openKolibri/halo-90/docs/artwork/cardBack.png

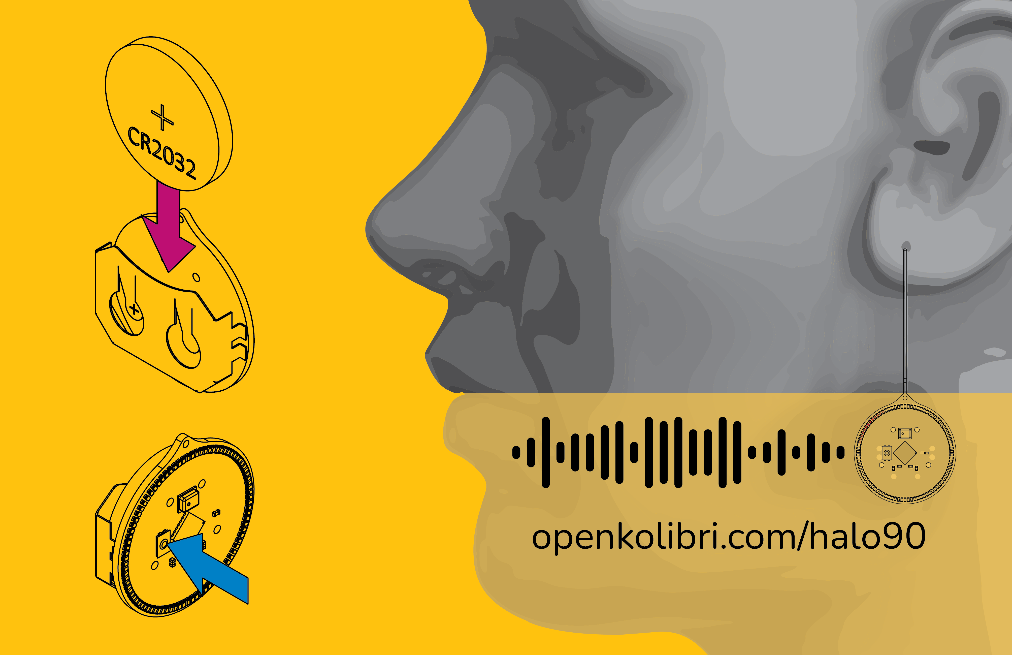
docs/artwork/cardBack.png
