openKolibri/halo-90/docs/artwork/cardFront.png

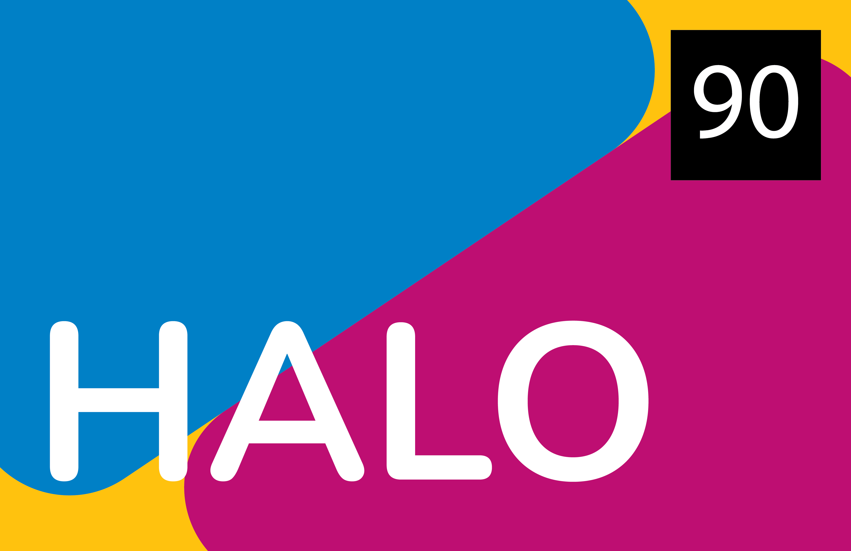
docs/artwork/cardFront.png
