openKolibri/halo-90/docs/case/batch.jpg

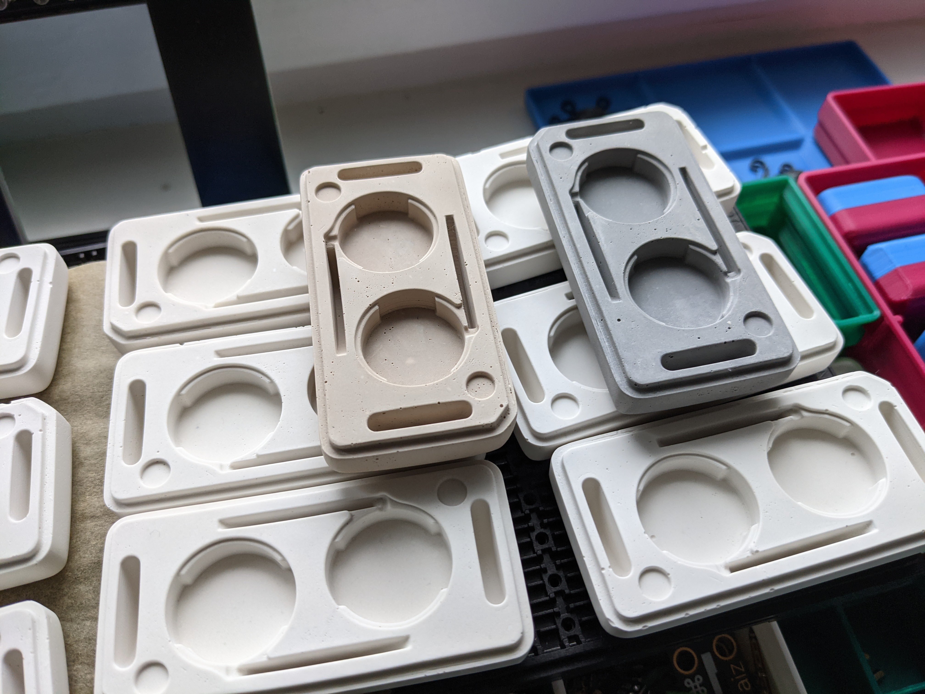
docs/case/batch.jpg
