openKolibri/halo-90/docs/case/caseRender.jpg

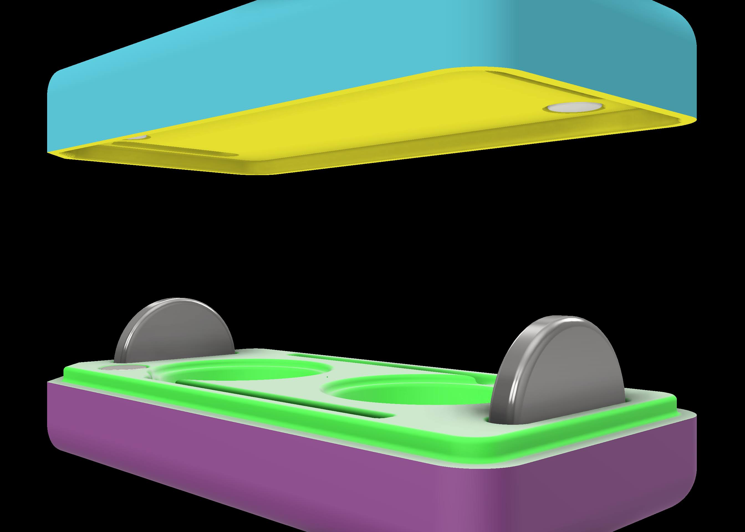
docs/case/caseRender.jpg
