openKolibri/halo-90/docs/case/cases.jpg

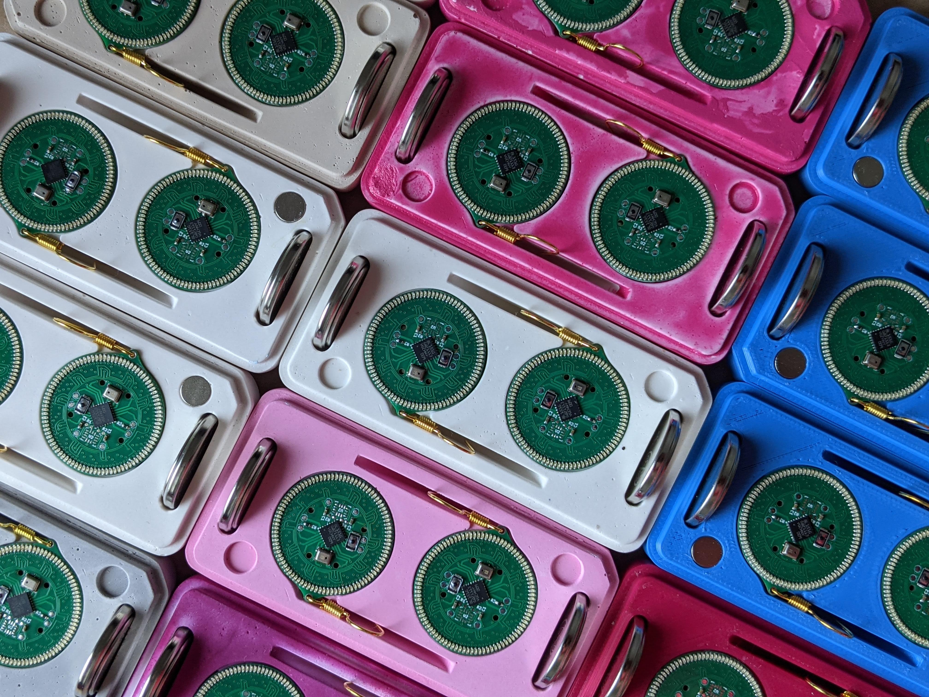
docs/case/cases.jpg
