openKolibri/halo-90/docs/case/casting.jpg

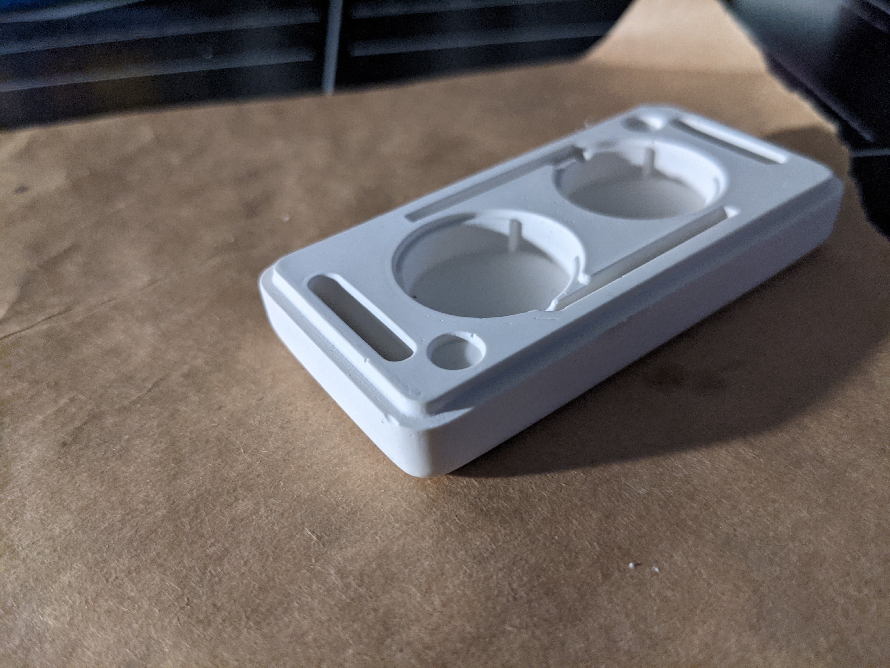
docs/case/casting.jpg
