openKolibri/halo-90/docs/case/master.jpg

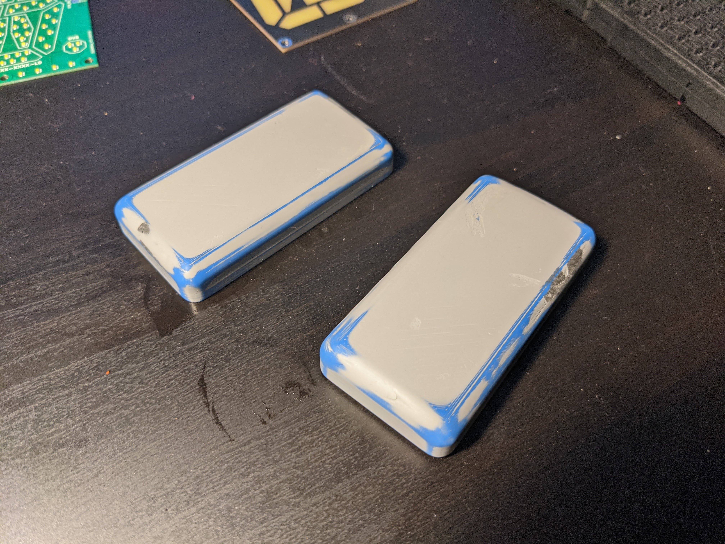
docs/case/master.jpg
