openKolibri/halo-90/docs/case/mould.jpg

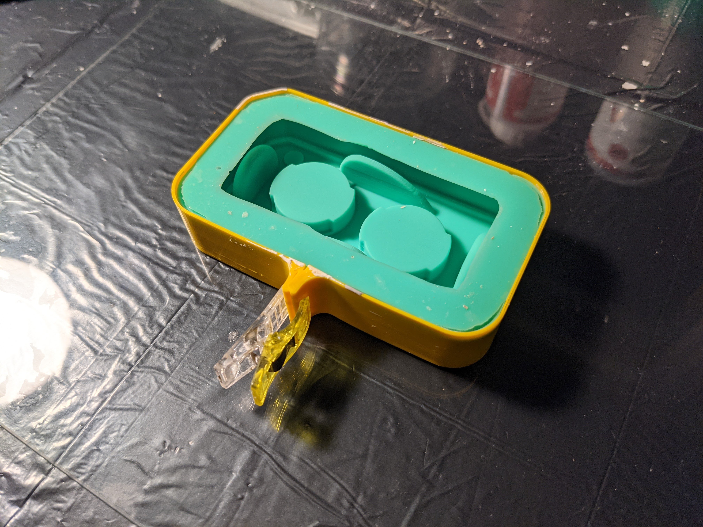
docs/case/mould.jpg
