openKolibri/halo-90/docs/connectors/mass.jpg

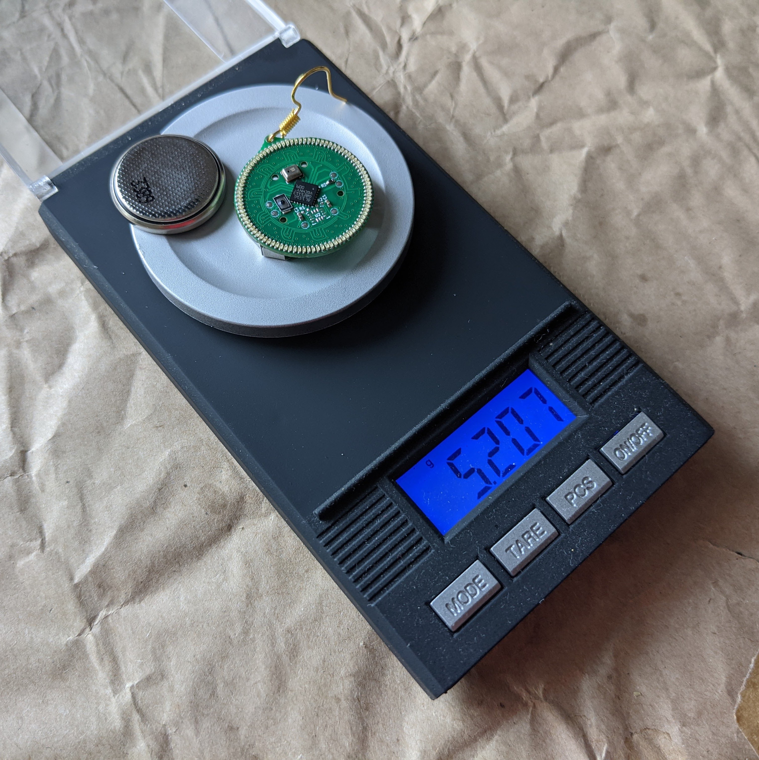
docs/connectors/mass.jpg
