openKolibri/halo-90/docs/connectors/pinDim.jpg

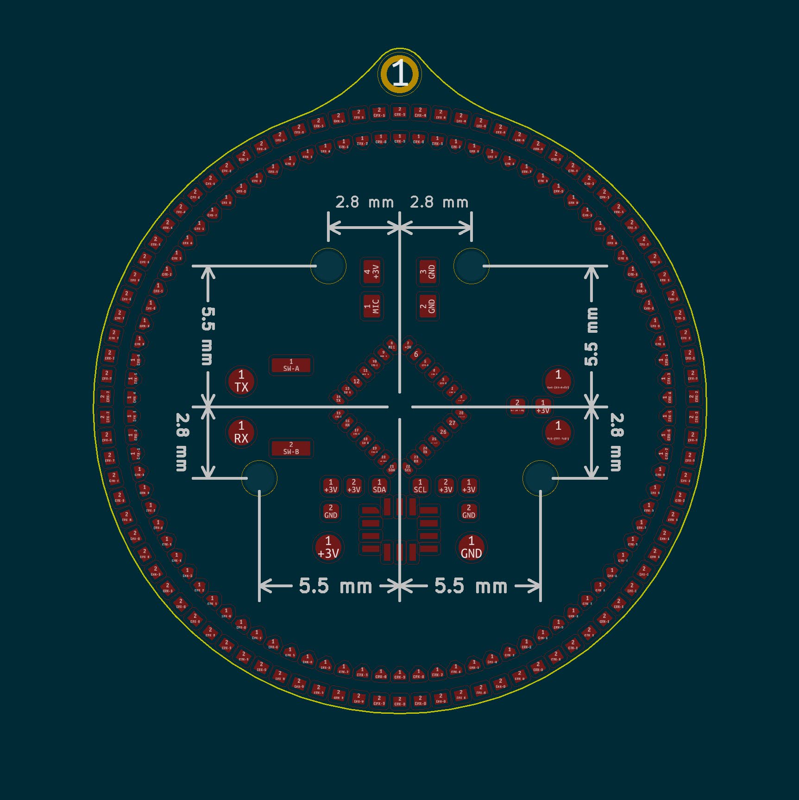
docs/connectors/pinDim.jpg
