openKolibri/halo-90/docs/firmware/boot.gif

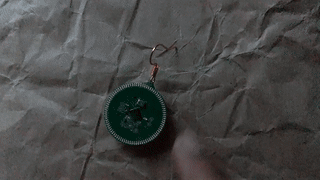
docs/firmware/boot.gif
