openKolibri/halo-90/docs/firmware/powerProfile/audio.gif

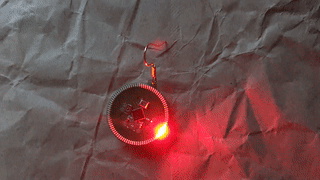
docs/firmware/powerProfile/audio.gif
