openKolibri/halo-90/docs/firmware/powerProfile/audioPowerProfile.png

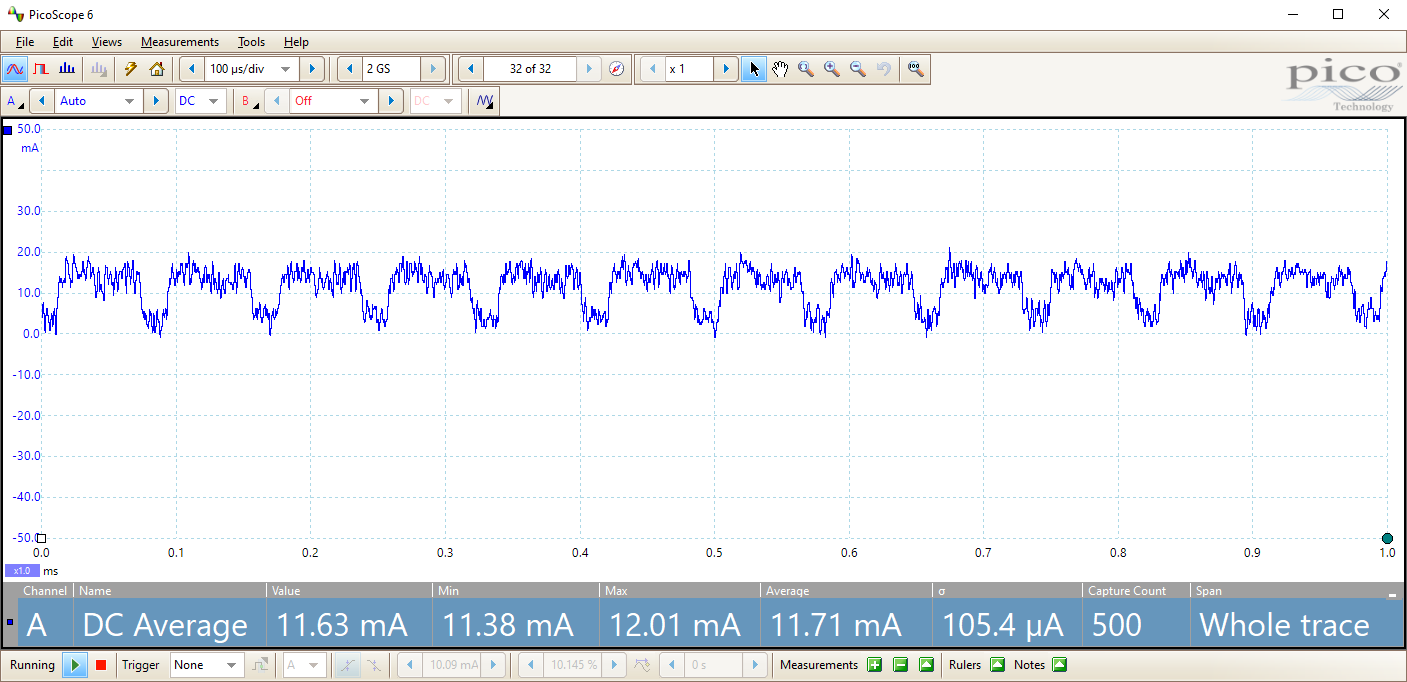
docs/firmware/powerProfile/audioPowerProfile.png
