openKolibri/halo-90/docs/firmware/powerProfile/halo.gif

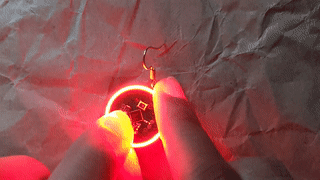
docs/firmware/powerProfile/halo.gif
