openKolibri/halo-90/docs/firmware/powerProfile/haloPowerProfile.png

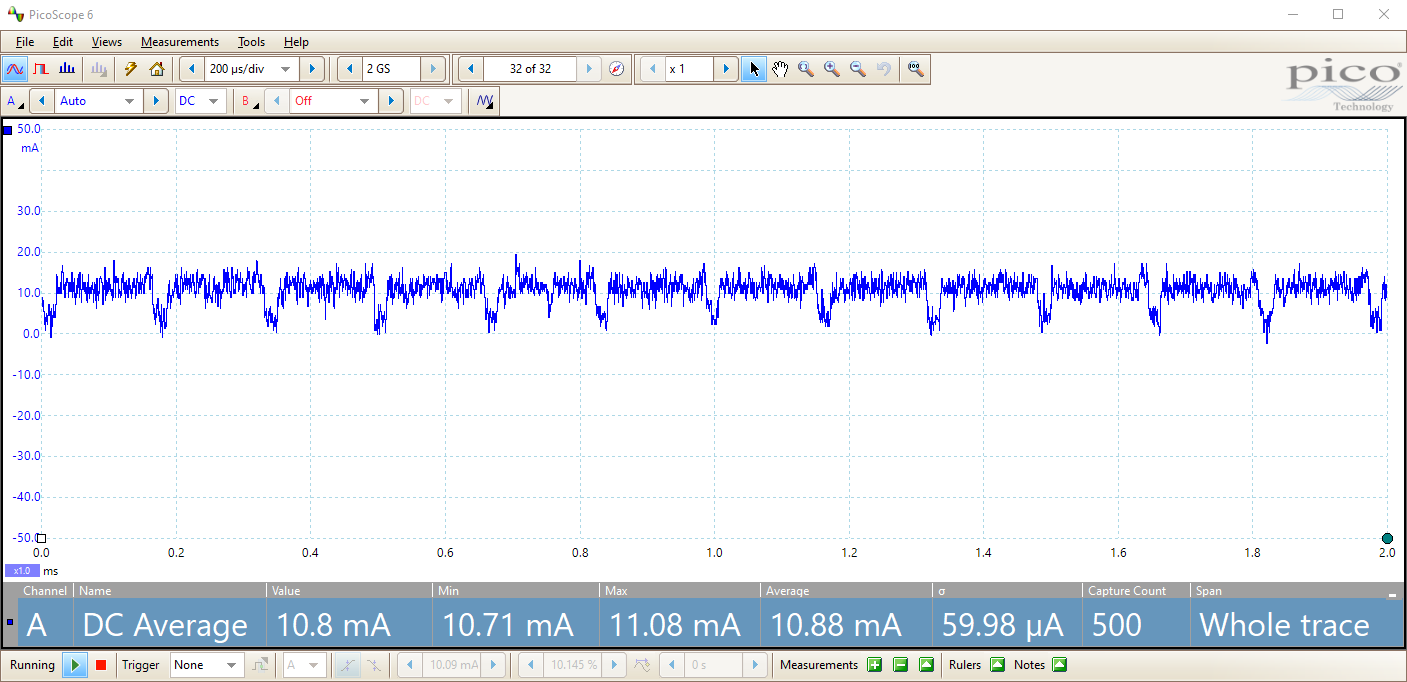
docs/firmware/powerProfile/haloPowerProfile.png
