openKolibri/halo-90/docs/firmware/powerProfile/sparkle.gif

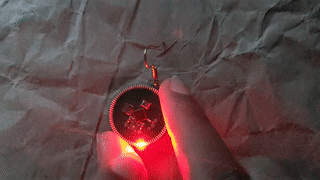
docs/firmware/powerProfile/sparkle.gif
