openKolibri/halo-90/docs/firmware/powerProfile/sparklePowerProfile.png

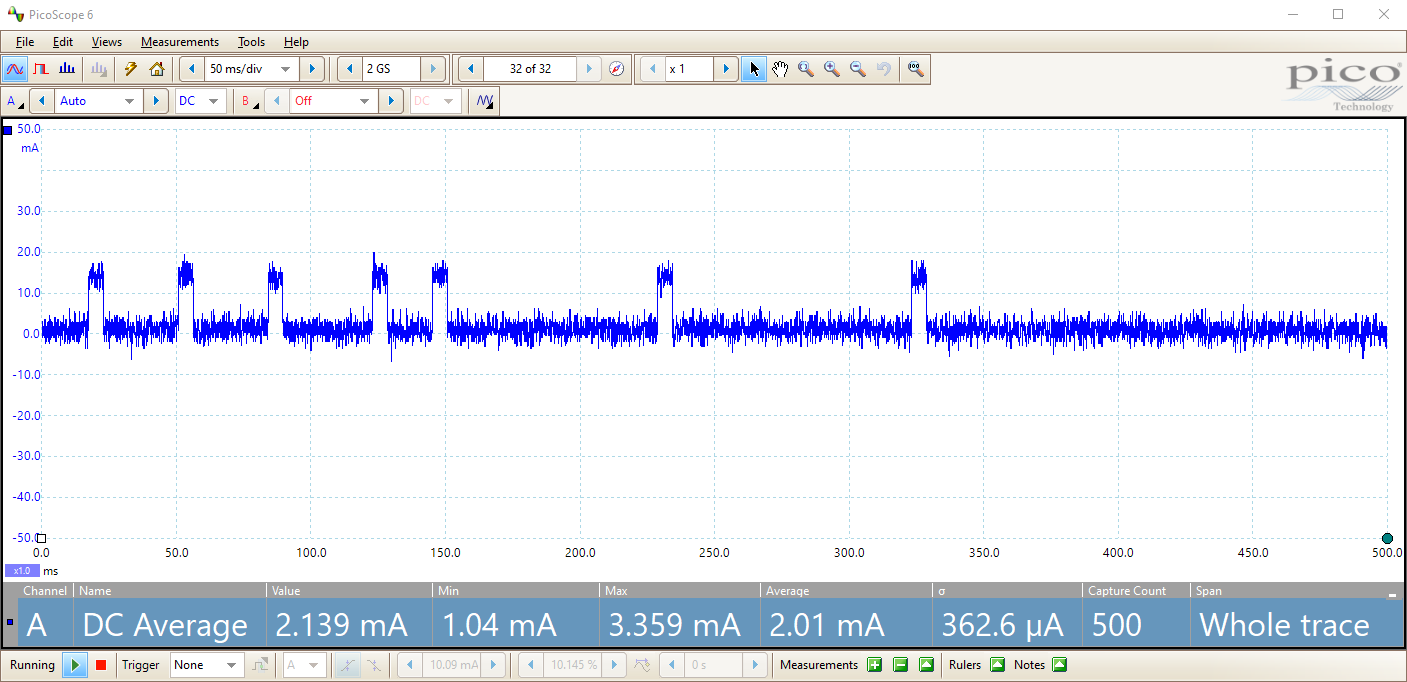
docs/firmware/powerProfile/sparklePowerProfile.png
