openKolibri/halo-90/docs/intro/haloSetDisplay.jpg

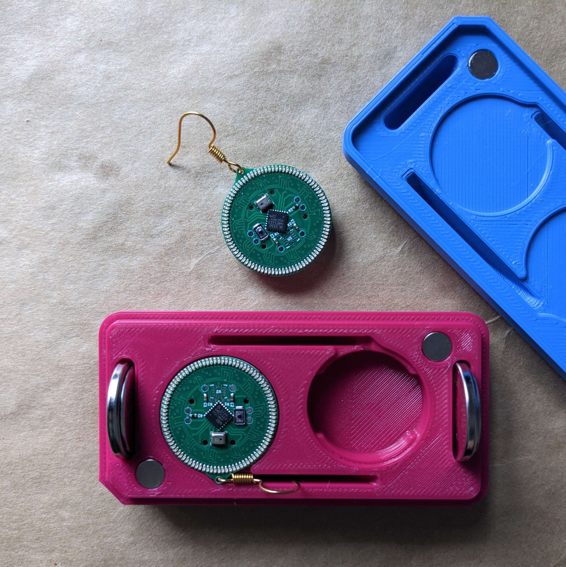
docs/intro/haloSetDisplay.jpg
