openKolibri/halo-90/docs/layers/L0.png

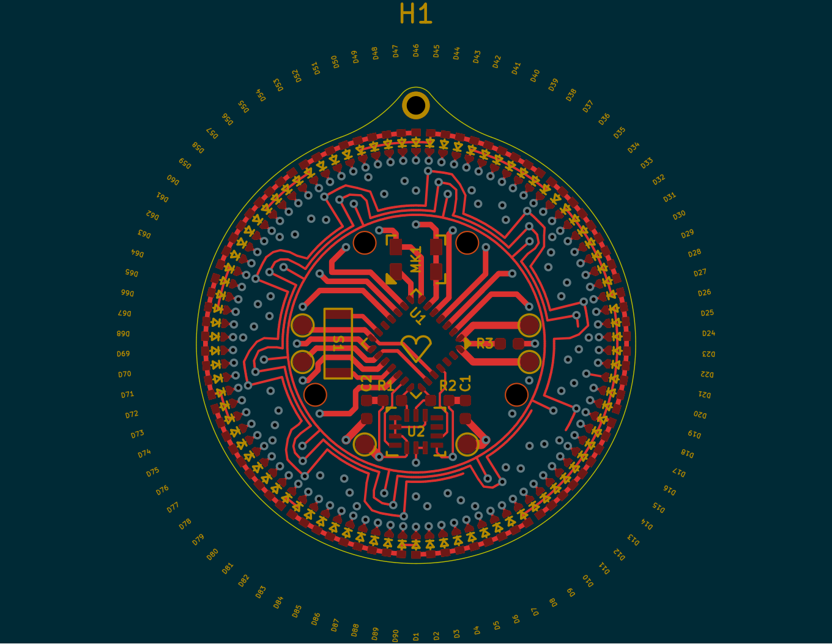
docs/layers/L0.png
