openKolibri/halo-90/docs/layers/L1.png

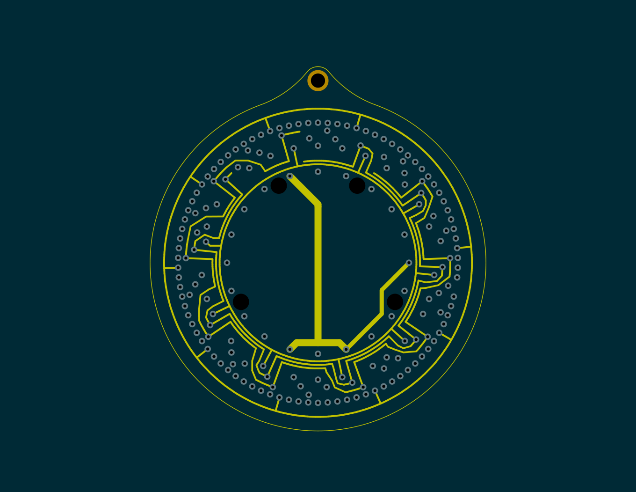
docs/layers/L1.png
