openKolibri/halo-90/docs/layers/L2.png

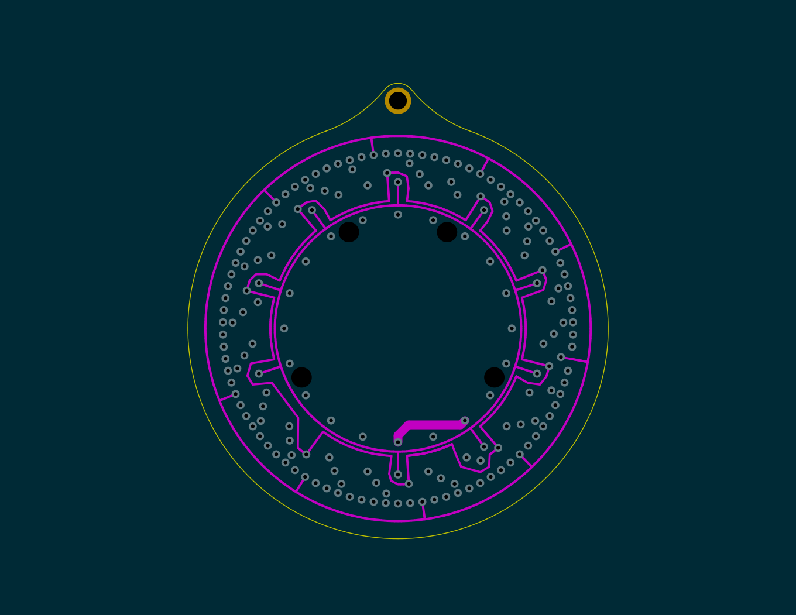
docs/layers/L2.png
