openKolibri/halo-90/docs/layers/L3.png

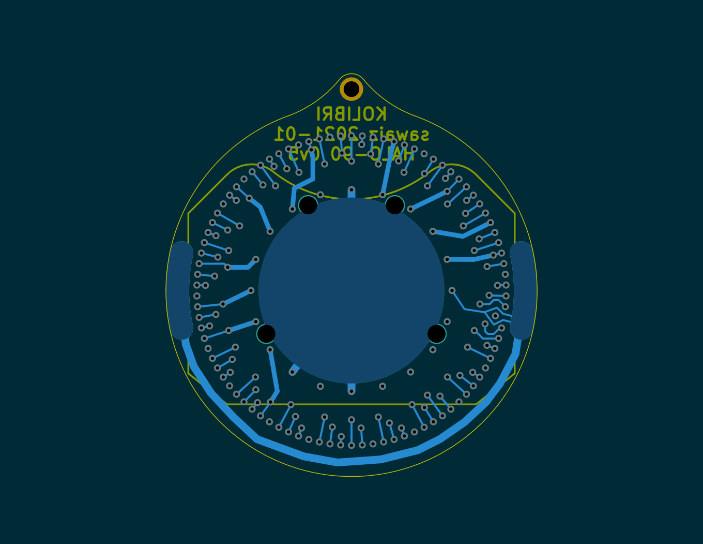
docs/layers/L3.png
