openKolibri/halo-90/docs/patterns/halo.gif

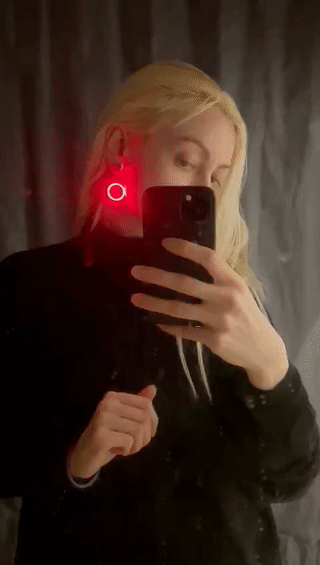
docs/patterns/halo.gif
