openKolibri/halo-90/docs/programmer.jpg

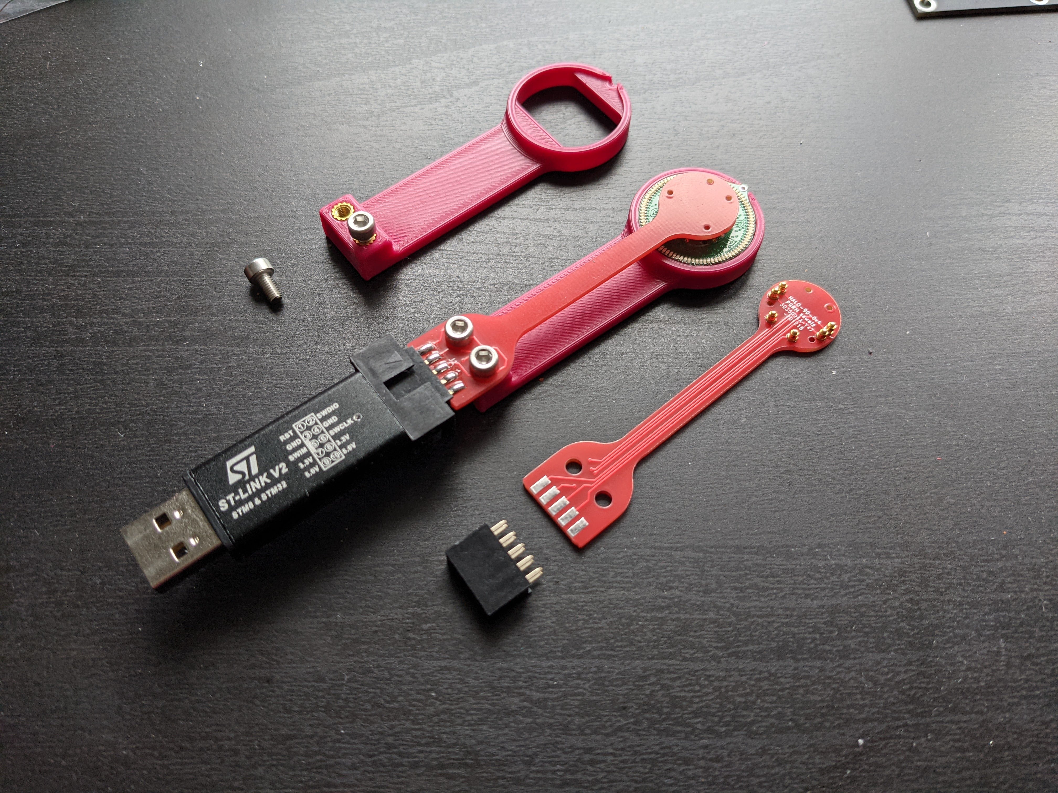
docs/programmer.jpg
