openKolibri/halo-90/docs/render.jpg

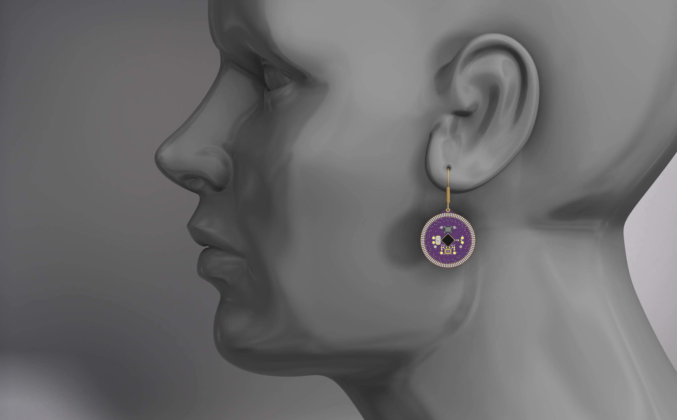
docs/render.jpg
