openKolibri/halo-90/docs/components/magnets.jpg

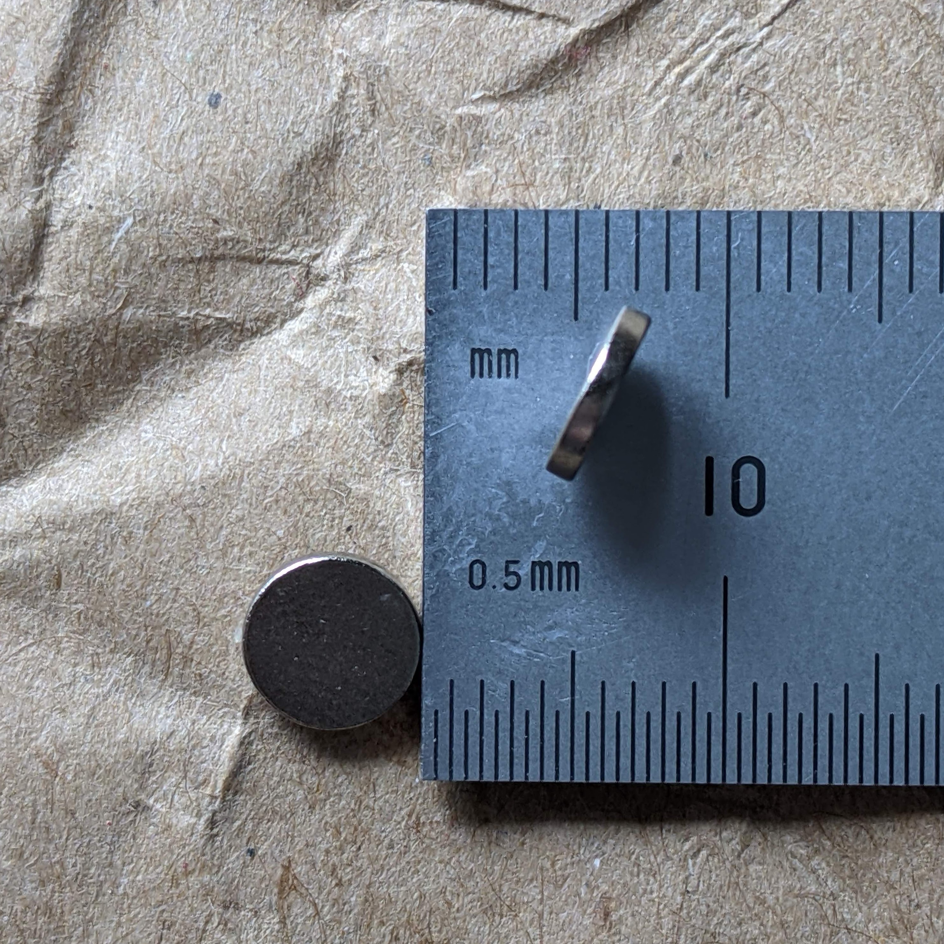
docs/components/magnets.jpg
