openKolibri/halo-90/pcb/components/BAT-HLD-001/BAT-HLD-001.jpg

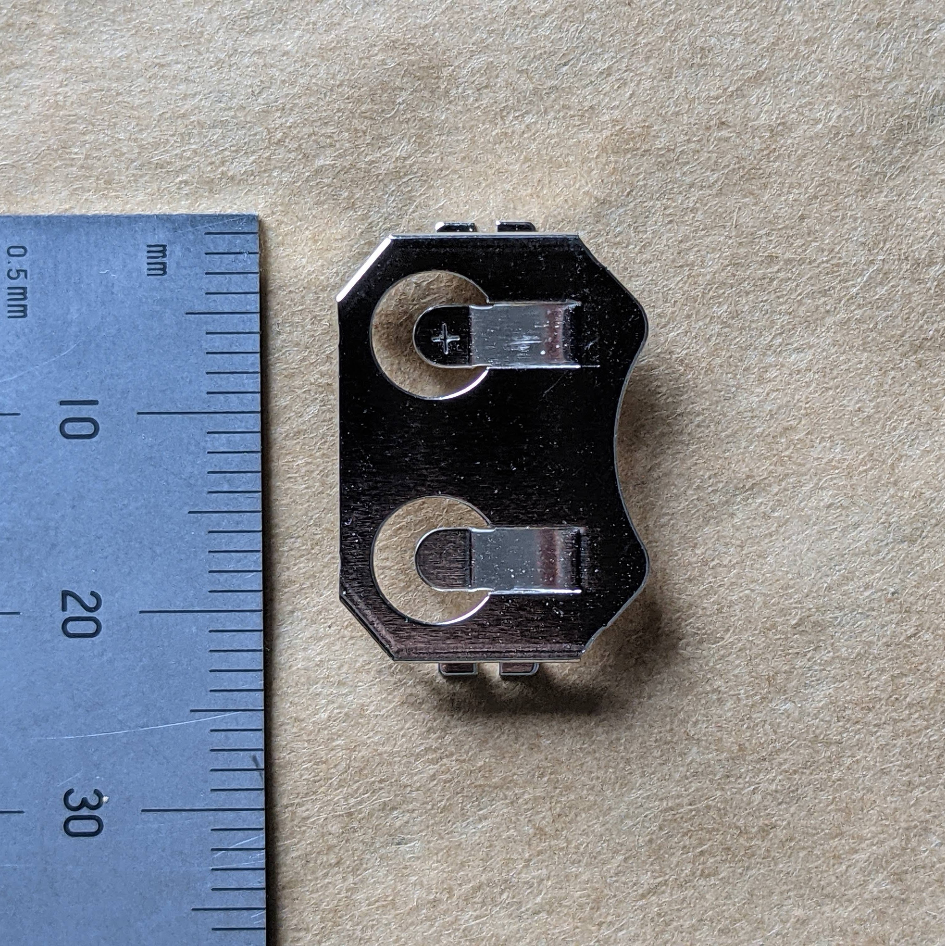
pcb/components/BAT-HLD-001/BAT-HLD-001.jpg
