openKolibri/halo-90/pcb/components/frenchEarwire/frenchEarwire.jpg

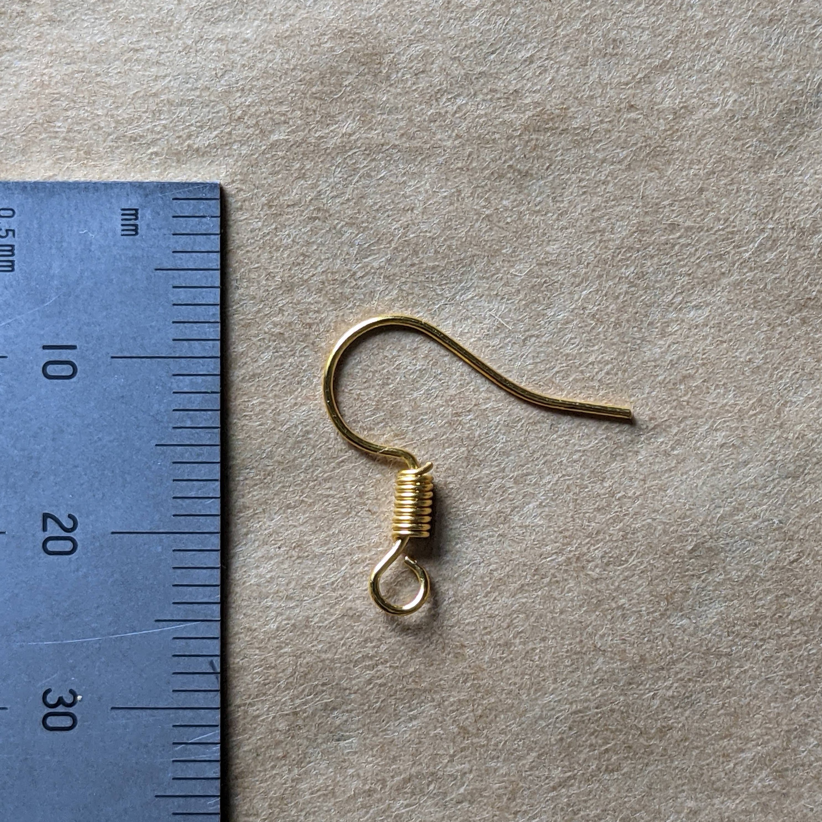
pcb/components/frenchEarwire/frenchEarwire.jpg
