openKolibri/halo-90/pcb/components/KXT3/KXT3.jpg

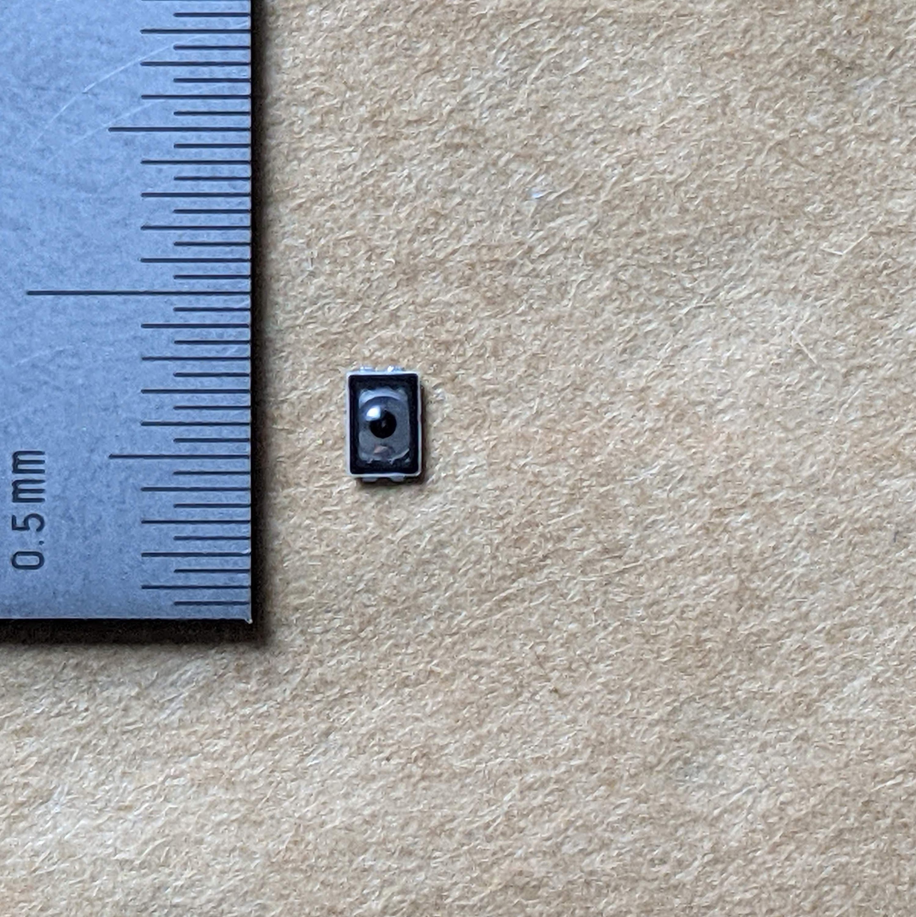
pcb/components/KXT3/KXT3.jpg
