openKolibri/halo-90/pcb/components/LSM6DSM/LSM6DSM.jpg

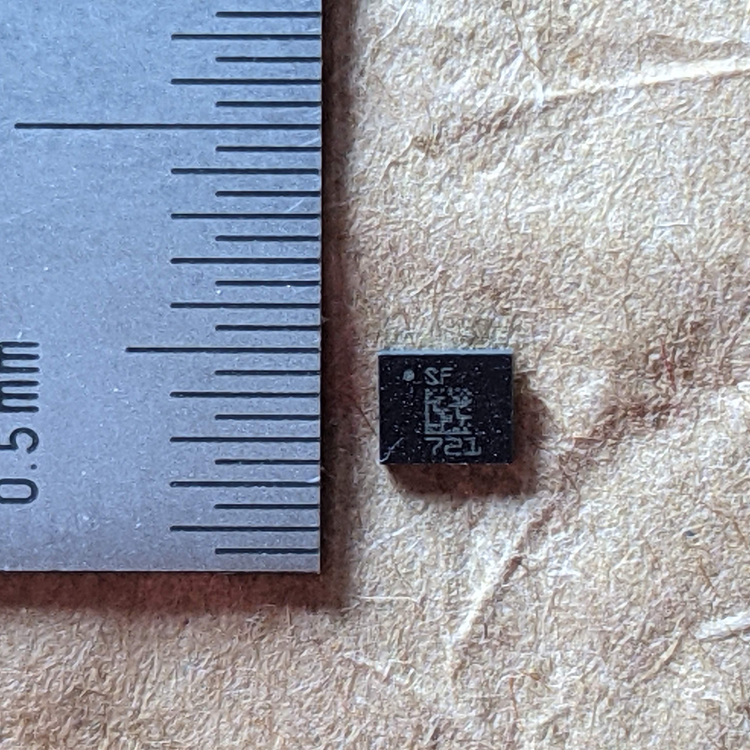
pcb/components/LSM6DSM/LSM6DSM.jpg
