openKolibri/halo-90/pcb/components/SPW2430HR5H-B/SPW2430HR5H-B.jpg

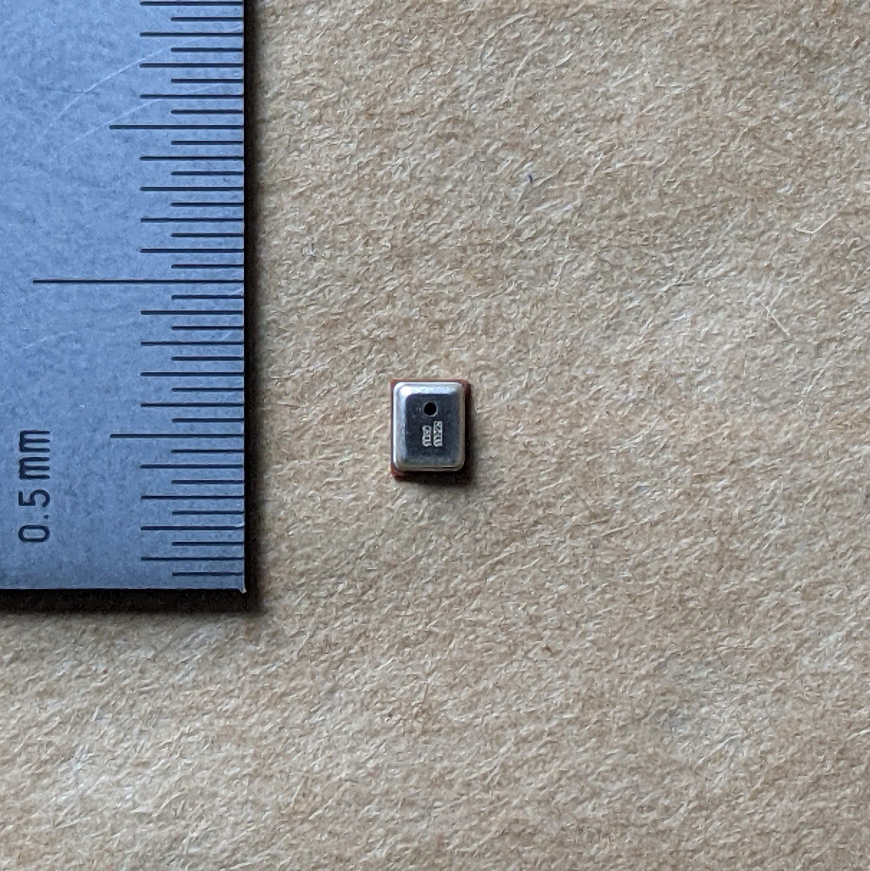
pcb/components/SPW2430HR5H-B/SPW2430HR5H-B.jpg
