openKolibri/halo-90/pcb/components/STM8L15xxx/STM8L15xxx.jpg

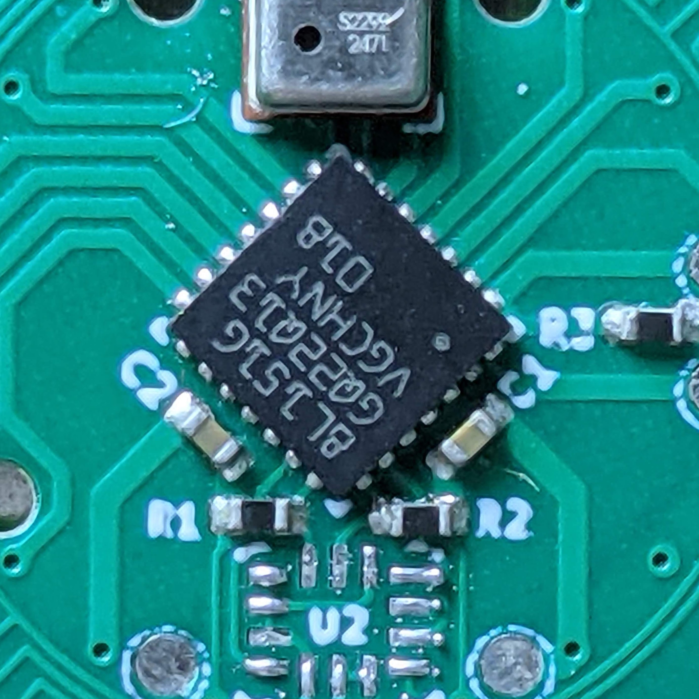
pcb/components/STM8L15xxx/STM8L15xxx.jpg
