openKolibri/halo-90/pcb/components/passives/L-0805.stp

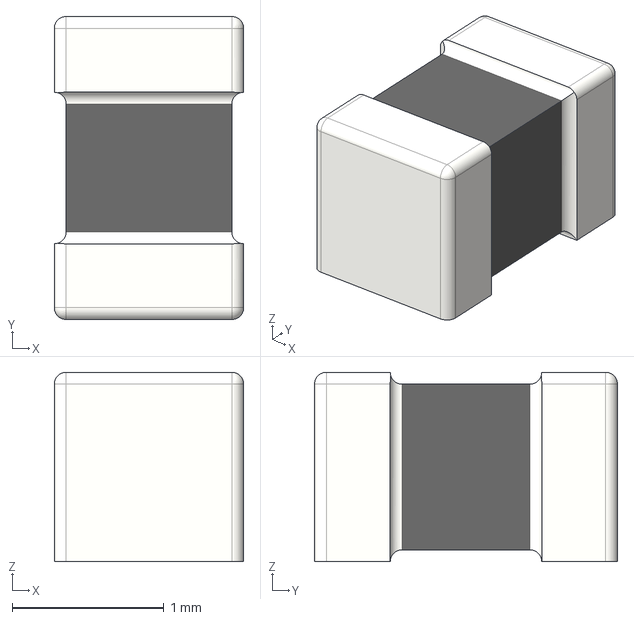
[picture p52: CAD file, 2021-01-04]
pcb/components/passives/L-0805.stp
1.25 x 2.00 x 1.25 mm
