openKolibri/halo-90/pcb/components/passives/C-0201.stp

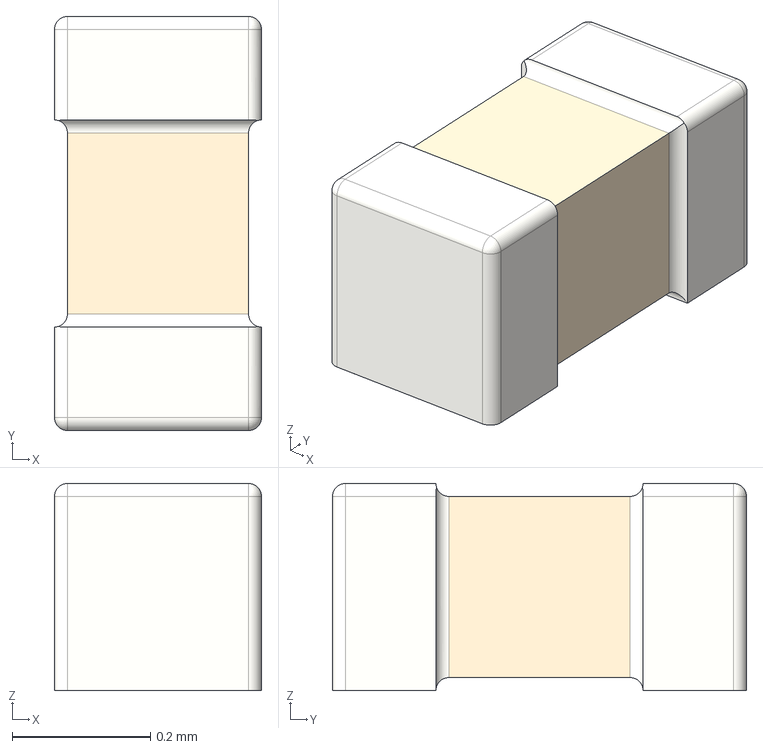
[picture p53: CAD file, 2021-01-04]
pcb/components/passives/C-0201.stp
0.3 x 0.6 x 0.3 mm
