openKolibri/halo-90/pcb/components/passives/R-0603.stp

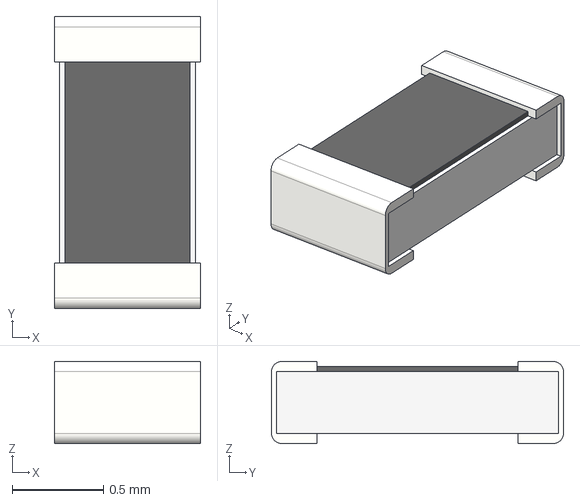
[picture p54: CAD file, 2021-01-04]
pcb/components/passives/R-0603.stp
0.8 x 1.60 x 0.45 mm
