openKolibri/halo-90/pcb/components/passives/L-0603.stp

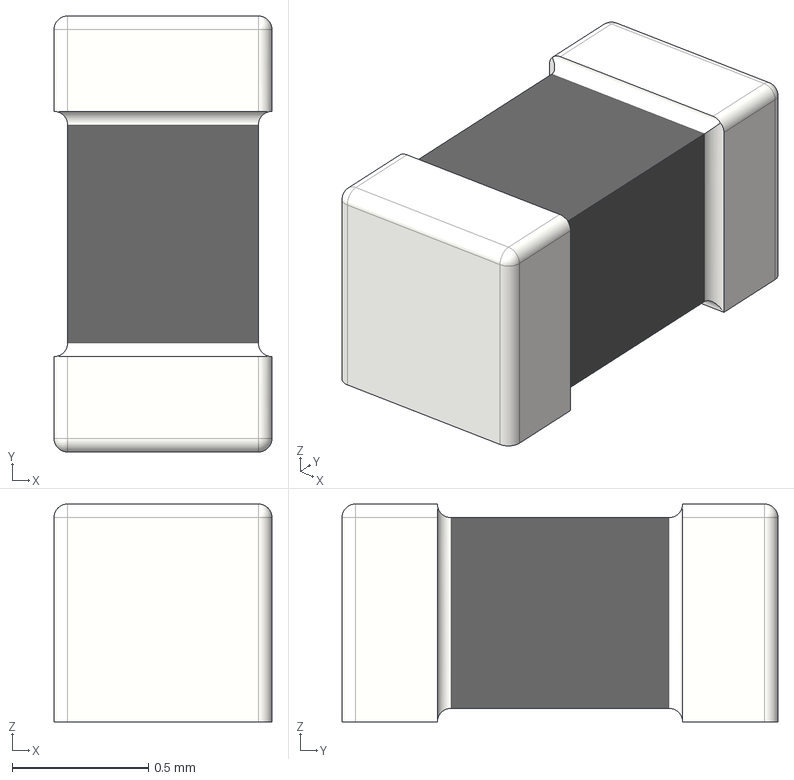
[picture p55: CAD file, 2021-01-04]
pcb/components/passives/L-0603.stp
0.8 x 1.60 x 0.8 mm
