openKolibri/halo-90/pcb/components/passives/C-2220.stp

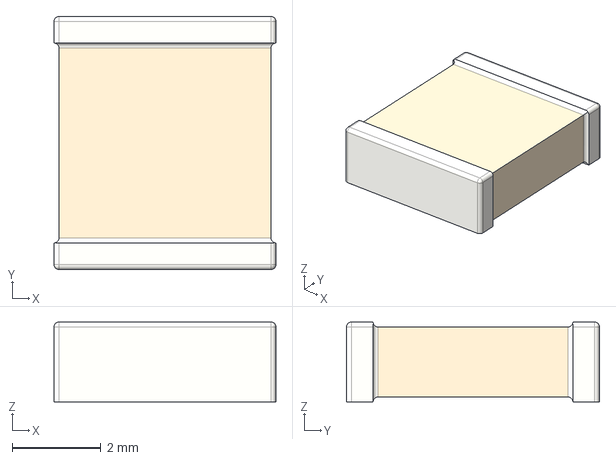
[picture p56: CAD file, 2021-01-04]
pcb/components/passives/C-2220.stp
5.00 x 5.70 x 1.80 mm
