openKolibri/halo-90/pcb/components/passives/C-0805.stp

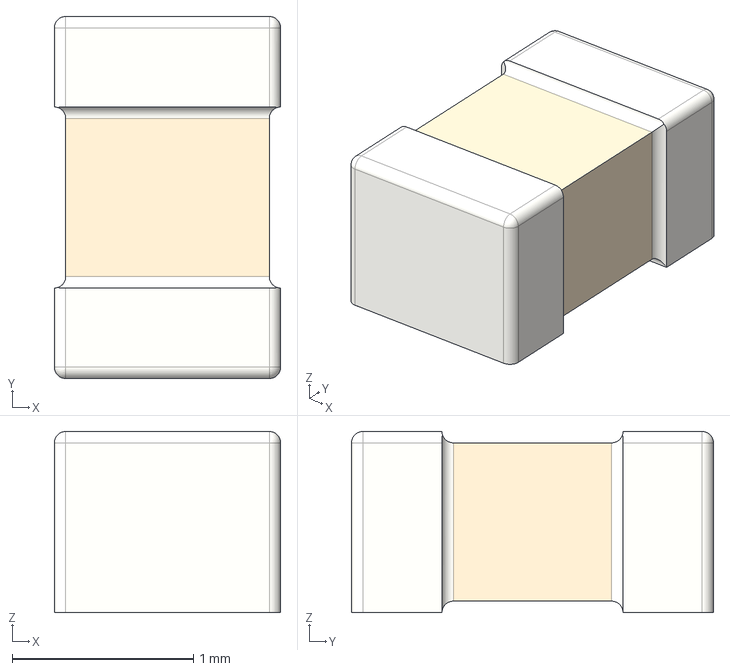
[picture p57: CAD file, 2021-01-04]
pcb/components/passives/C-0805.stp
1.25 x 2.00 x 1.00 mm
