openKolibri/halo-90/pcb/components/passives/R-1206.stp

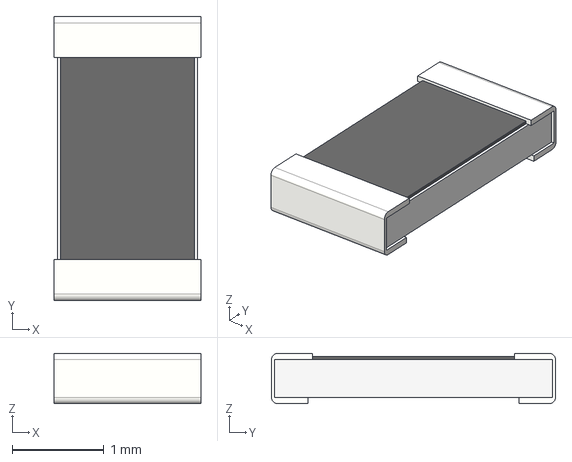
[picture p58: CAD file, 2021-01-04]
pcb/components/passives/R-1206.stp
1.60 x 3.10 x 0.55 mm
