openKolibri/halo-90/pcb/components/passives/C-1206.stp

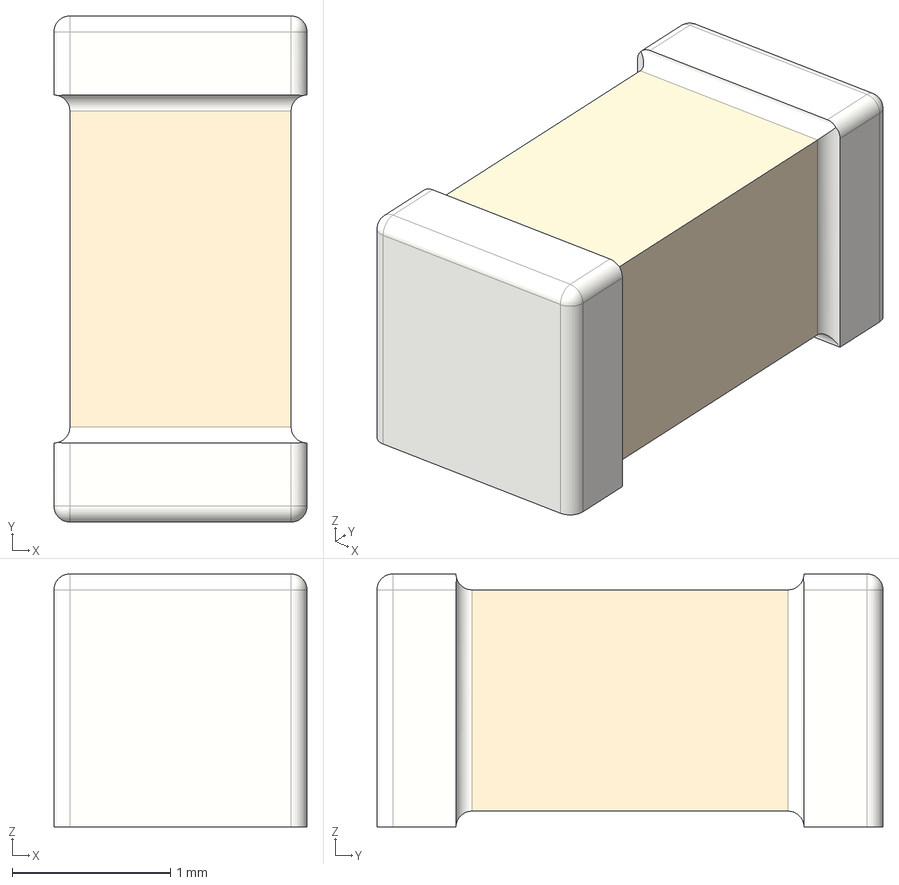
[picture p59: CAD file, 2021-01-04]
pcb/components/passives/C-1206.stp
1.60 x 3.20 x 1.60 mm
