openKolibri/halo-90/pcb/components/passives/R-0402.stp

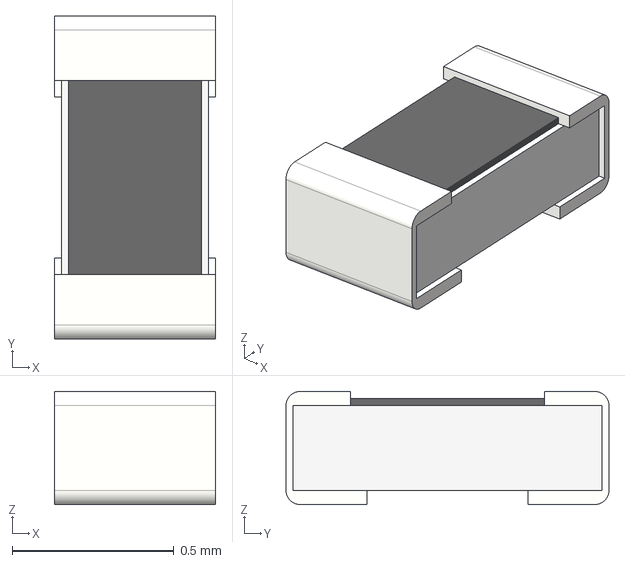
[picture p60: CAD file, 2021-01-04]
pcb/components/passives/R-0402.stp
0.5 x 1.00 x 0.35 mm
