openKolibri/halo-90/pcb/components/passives/R-0805.stp

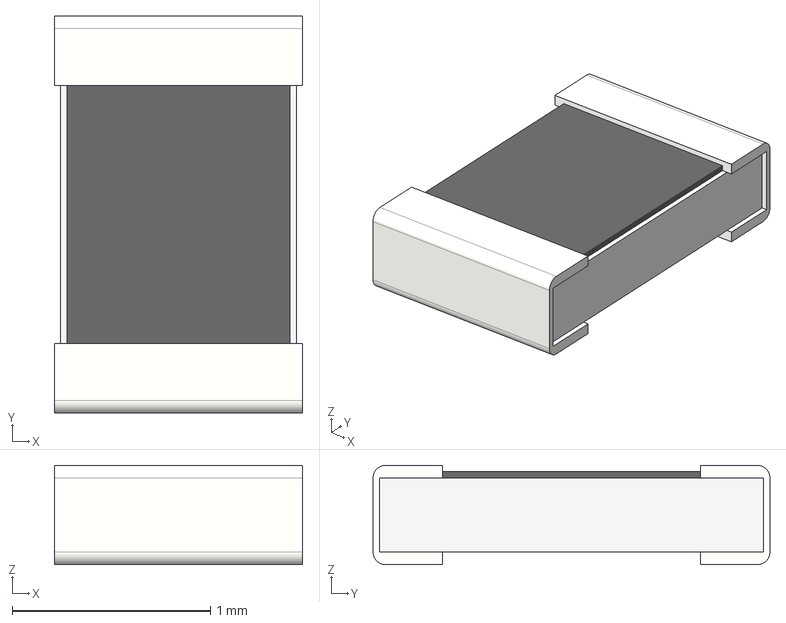
[picture p61: CAD file, 2021-01-04]
pcb/components/passives/R-0805.stp
1.25 x 2.00 x 0.5 mm
