openKolibri/halo-90/pcb/components/passives/C-1812.stp

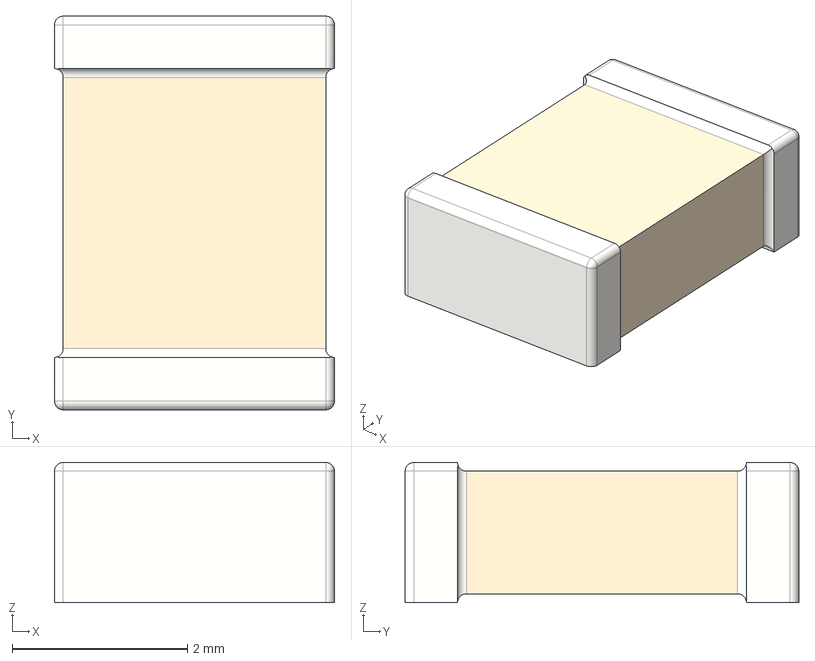
[picture p62: CAD file, 2021-01-04]
pcb/components/passives/C-1812.stp
3.20 x 4.50 x 1.60 mm
