openKolibri/halo-90/docs/assembly/jigs.jpg

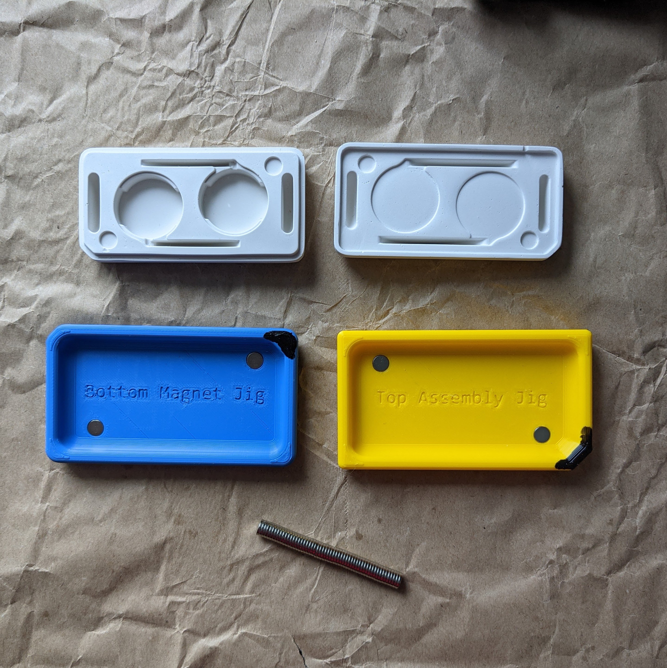
docs/assembly/jigs.jpg
