openKolibri/halo-90/docs/assembly/jigsGlue.jpg

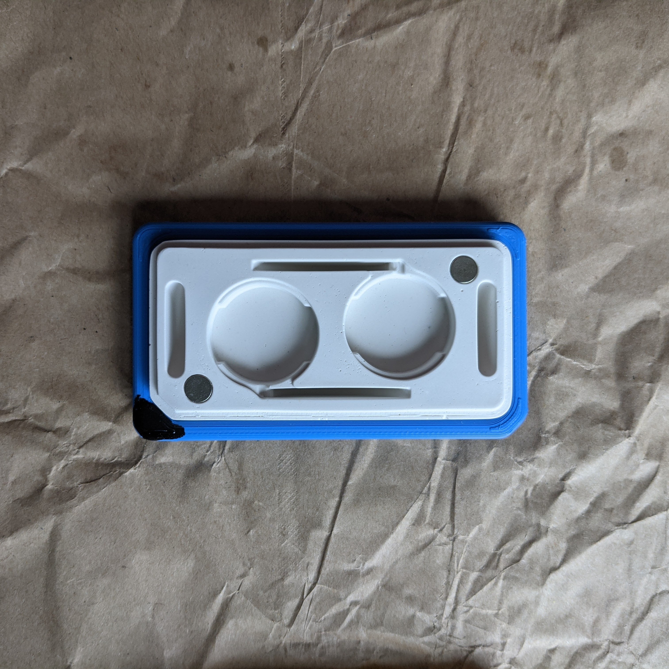
docs/assembly/jigsGlue.jpg
