openKolibri/halo-90/docs/case/fdmPrinted.jpg

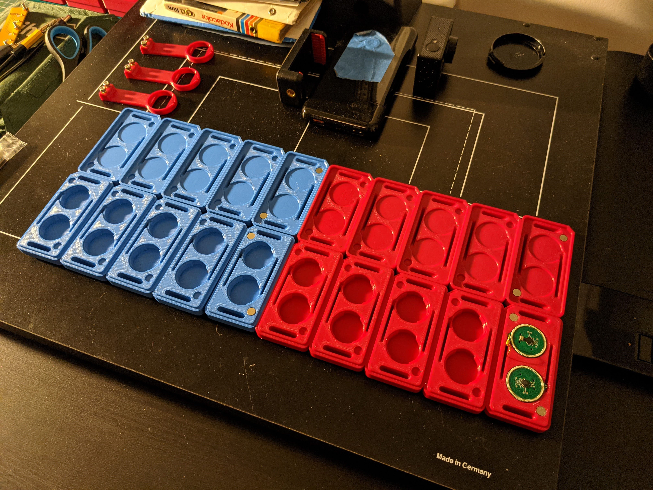
docs/case/fdmPrinted.jpg
