openKolibri/halo-90/docs/pcbAssembly/assemblyDraw.png

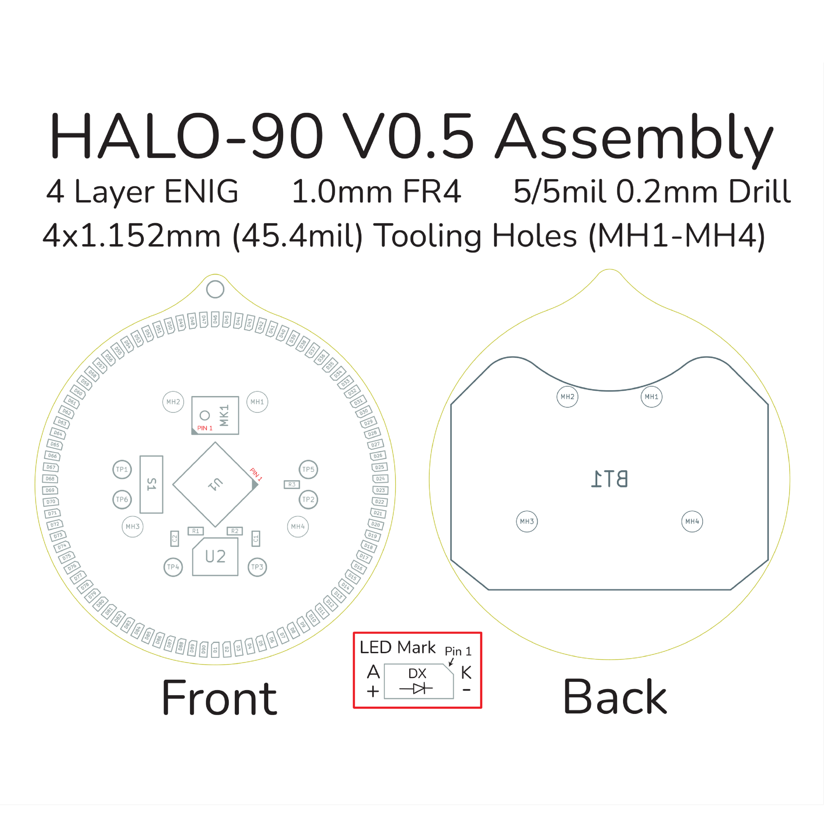
docs/pcbAssembly/assemblyDraw.png
