openKolibri/halo-90/docs/pcbAssembly/back-iso.jpg

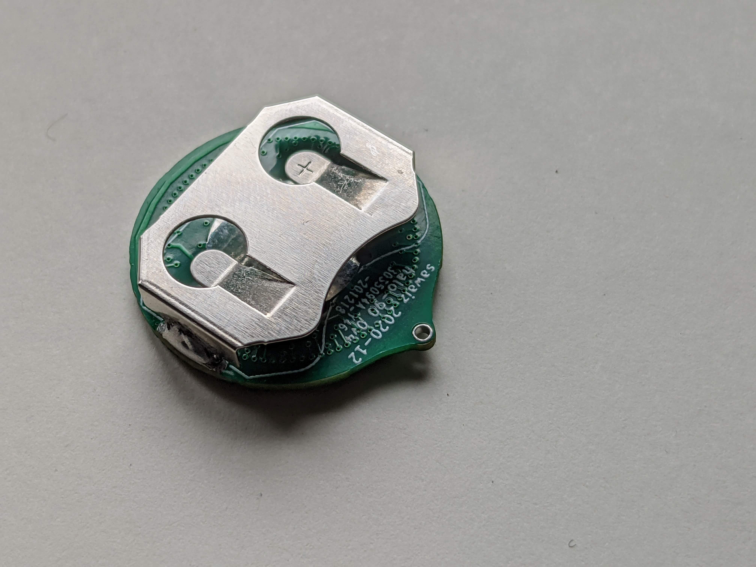
docs/pcbAssembly/back-iso.jpg
