openKolibri/halo-90/docs/pcbAssembly/front-detail.jpg

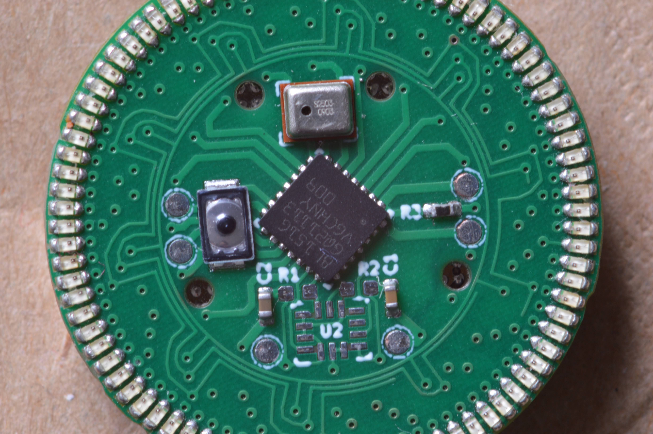
docs/pcbAssembly/front-detail.jpg
