openKolibri/halo-90/docs/pcbAssembly/front-full.jpg

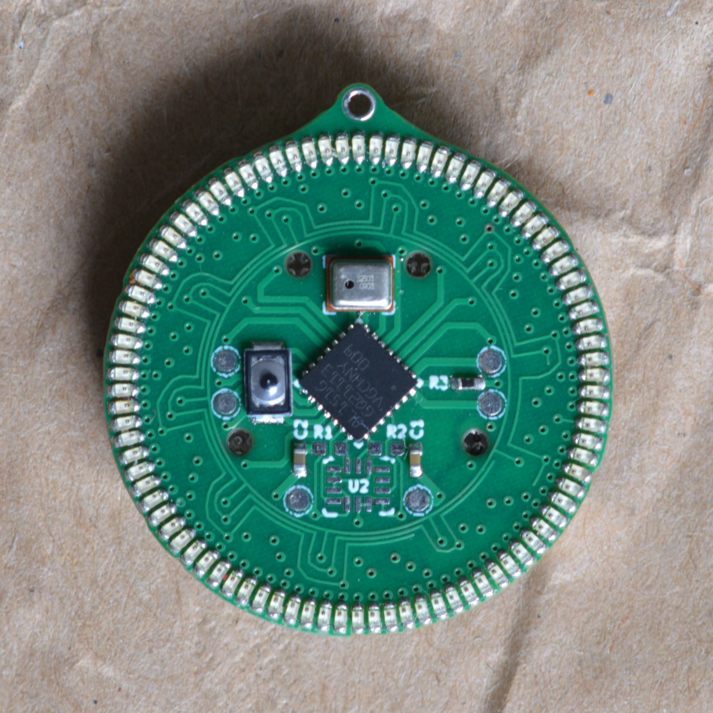
docs/pcbAssembly/front-full.jpg
