openKolibri/halo-90/docs/pcbAssembly/hexPackedPanel.png

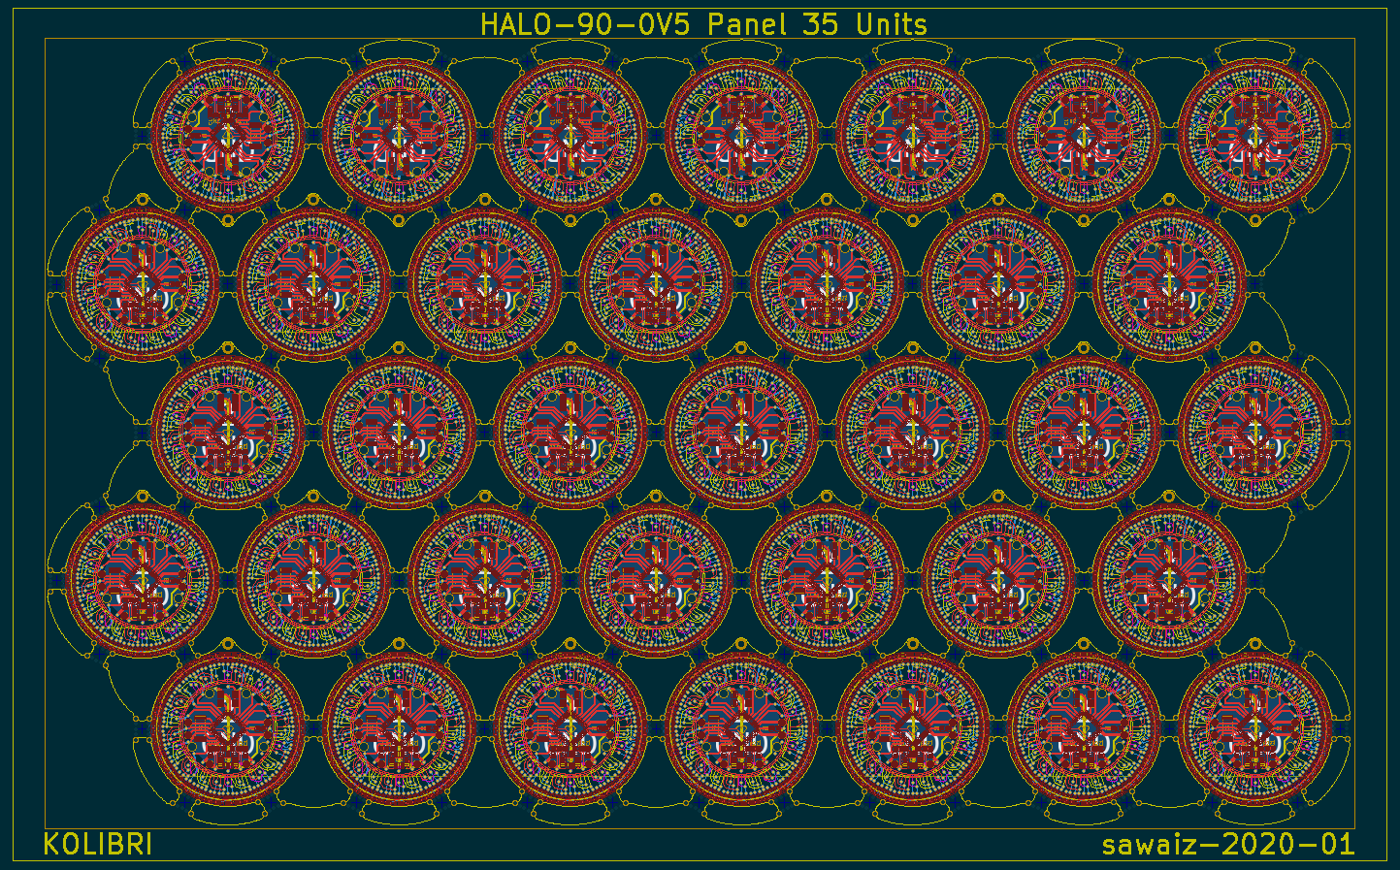
docs/pcbAssembly/hexPackedPanel.png
